ihsan92UM/Master_Thesis/graphics/clock_configuration.png

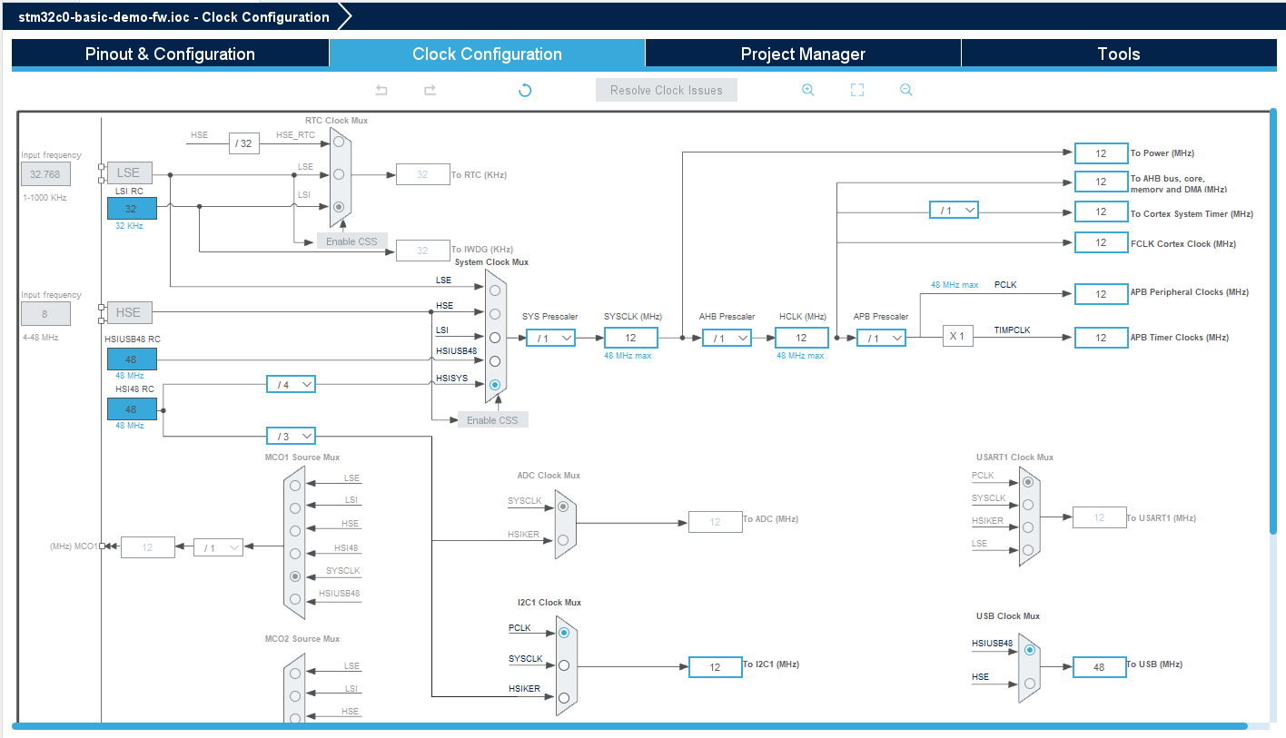
graphics/clock_configuration.png
