ihsan92UM/Master_Thesis/graphics/code_skeleton.png

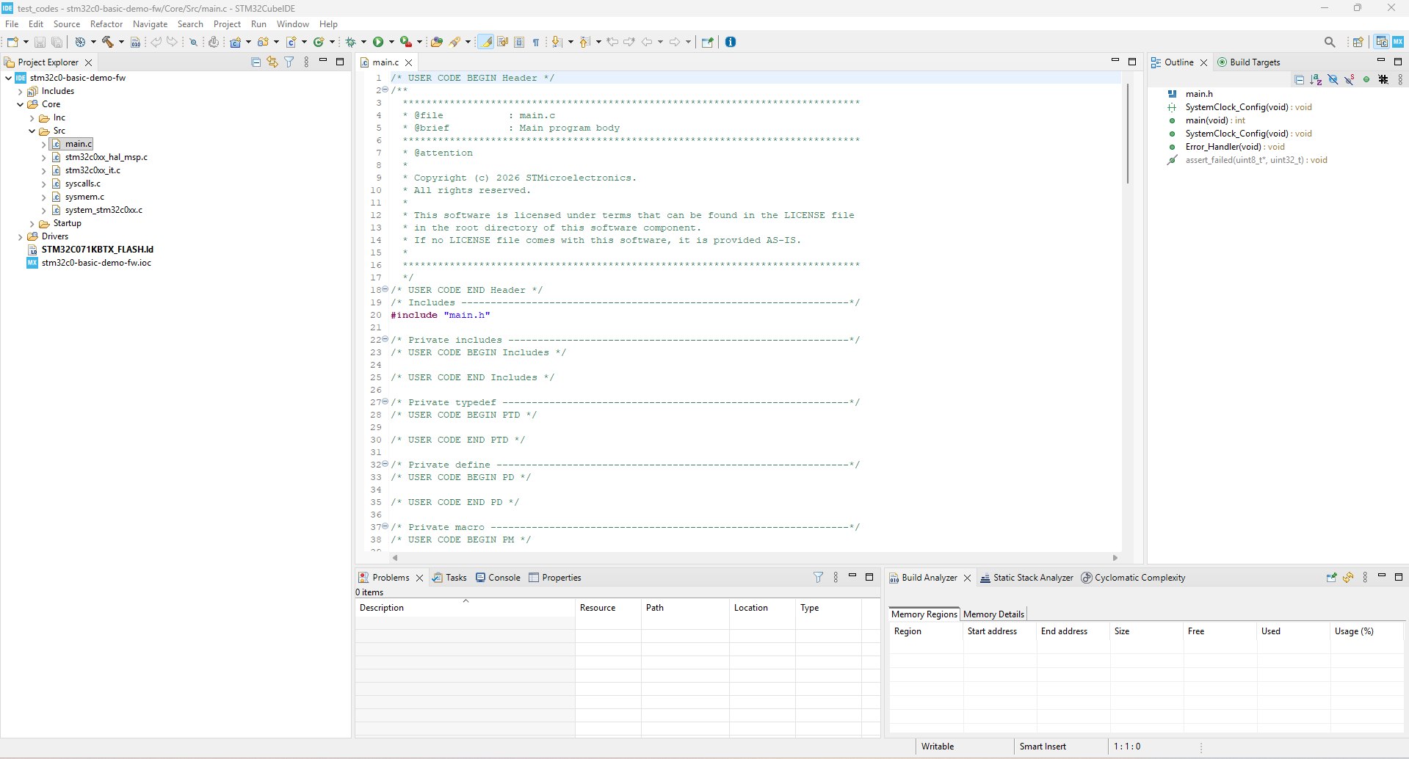
graphics/code_skeleton.png
