ihsan92UM/Master_Thesis/graphics/default_ioc.png

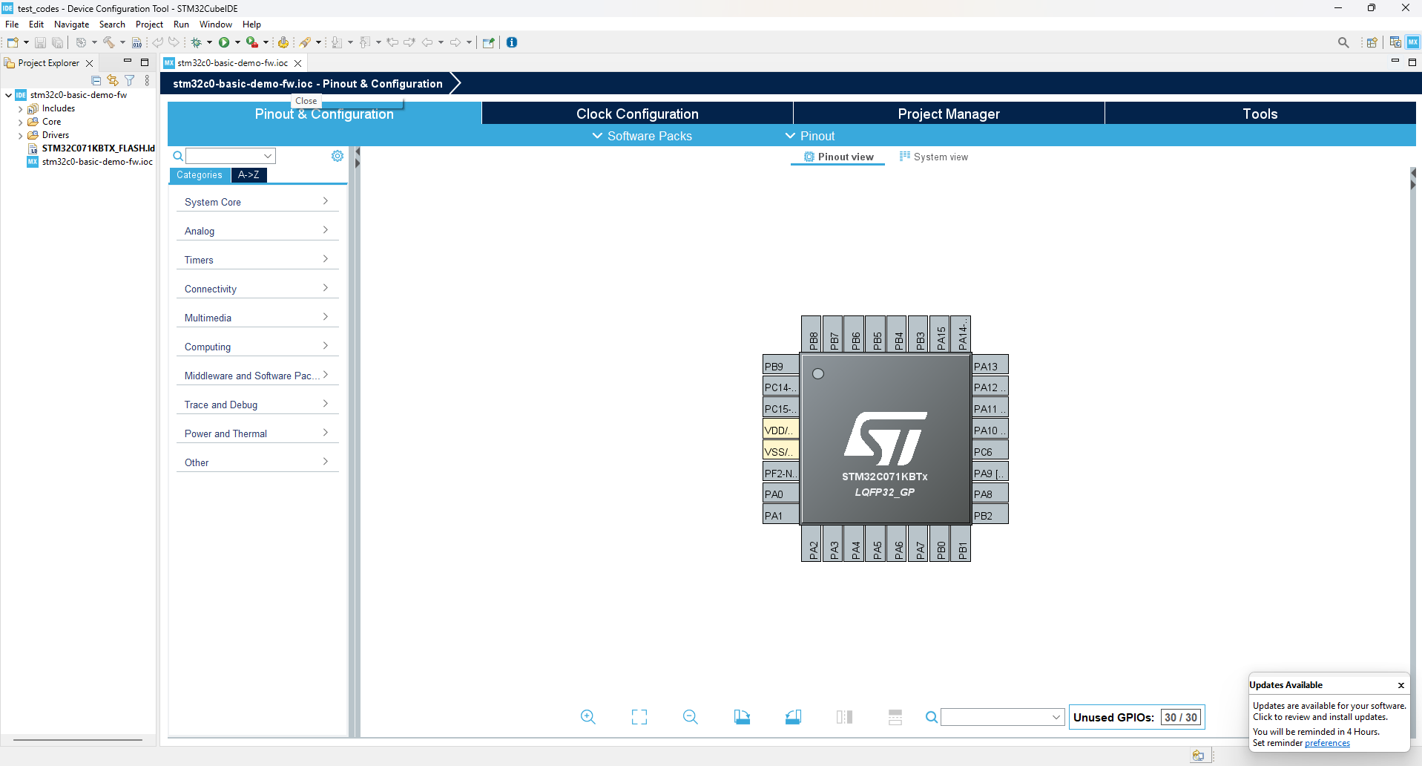
graphics/default_ioc.png
