ihsan92UM/Master_Thesis/graphics/file_name.png

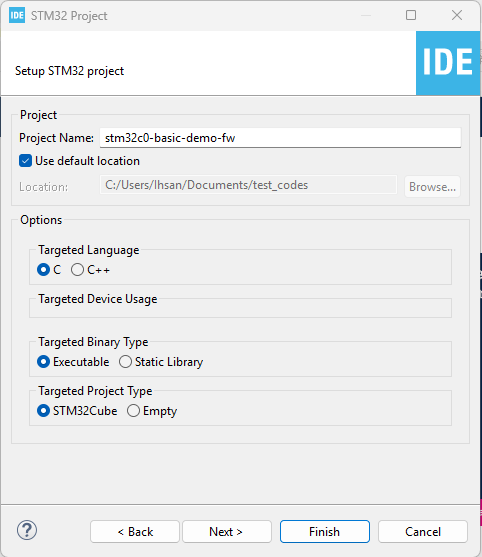
graphics/file_name.png
