ihsan92UM/Master_Thesis/graphics/generate_code.png

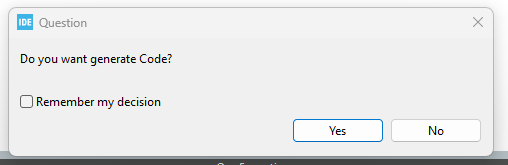
graphics/generate_code.png
