ihsan92UM/Master_Thesis/graphics/heap_stack_size.png

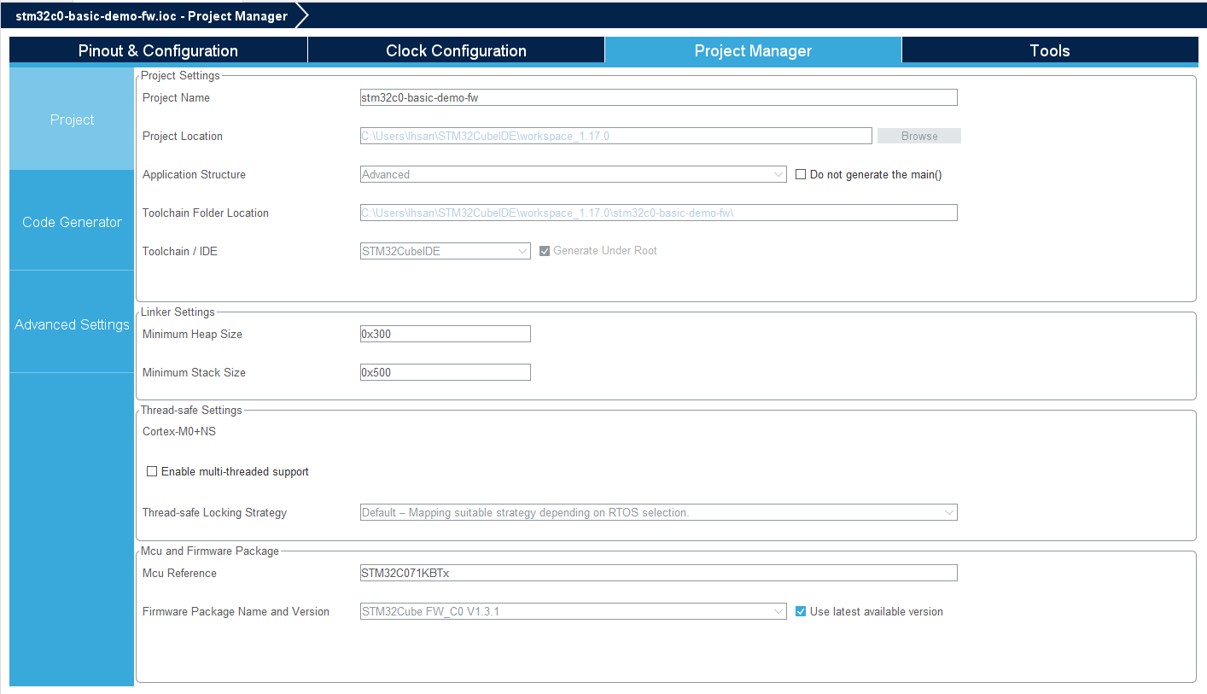
graphics/heap_stack_size.png
