ihsan92UM/Master_Thesis/graphics/perspective_open.png

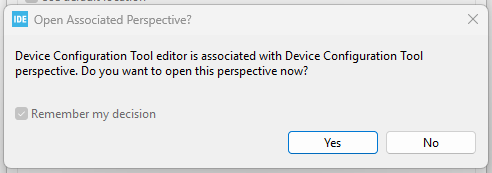
graphics/perspective_open.png
