ihsan92UM/Master_Thesis/graphics/target_selection.png

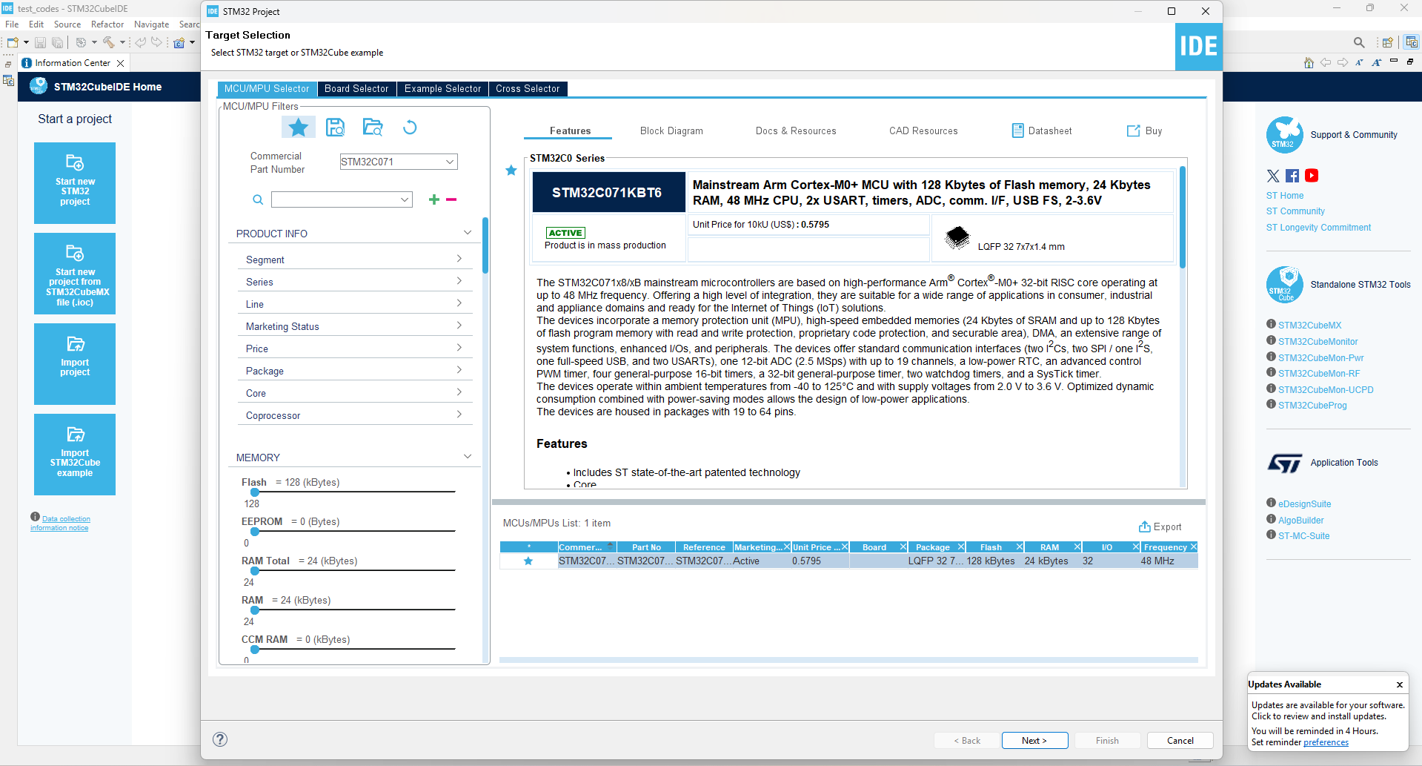
graphics/target_selection.png
