ihsan92UM/Master_Thesis/graphics/rcc_setup_ioc.png

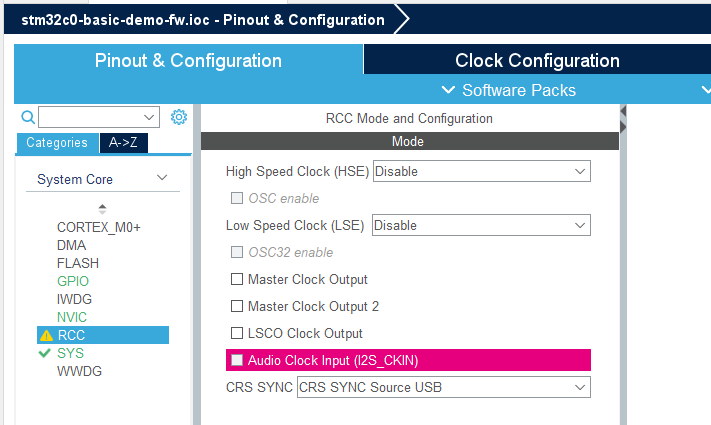
graphics/rcc_setup_ioc.png
