ihsan92UM/Master_Thesis/graphics/swd_setup_ioc.png

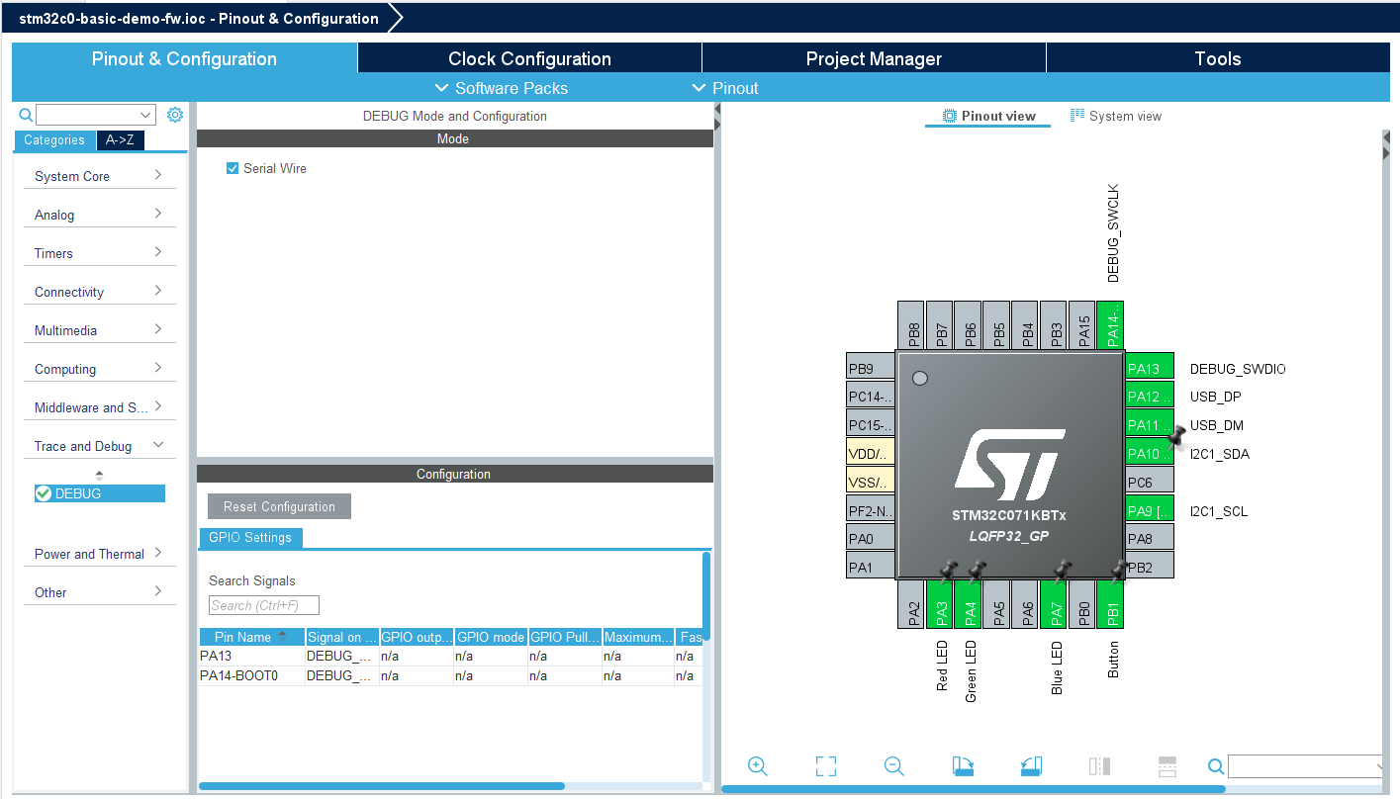
graphics/swd_setup_ioc.png
