ihsan92UM/Master_Thesis/stm32c0_codes/stm32c0-basic-demo-fw/Core/Inc/main.h

#define Red_LED_Pin GPIO_PIN_3
#define Red_LED_GPIO_Port GPIOA
#define Green_LED_Pin GPIO_PIN_4
#define Green_LED_GPIO_Port GPIOA
#define Blue_LED_Pin GPIO_PIN_7
#define Blue_LED_GPIO_Port GPIOA
#define Button_Pin GPIO_PIN_1
#define Button_GPIO_Port GPIOB
